Smeltie/Hyperion/Rendered Images/1.jpg

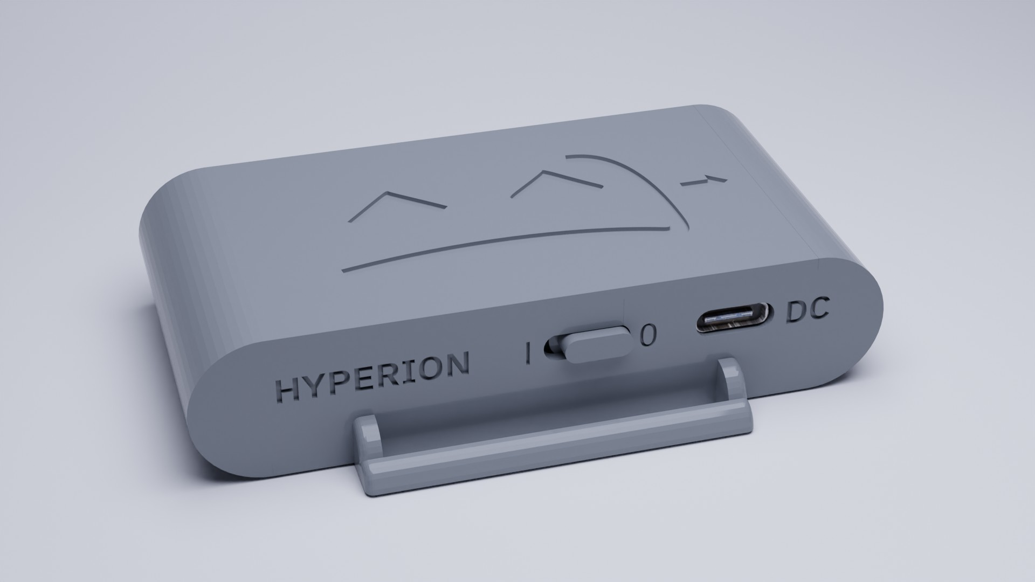
Rendered Images/1.jpg
