Smeltie/Hyperion/Rendered Images/2.jpg

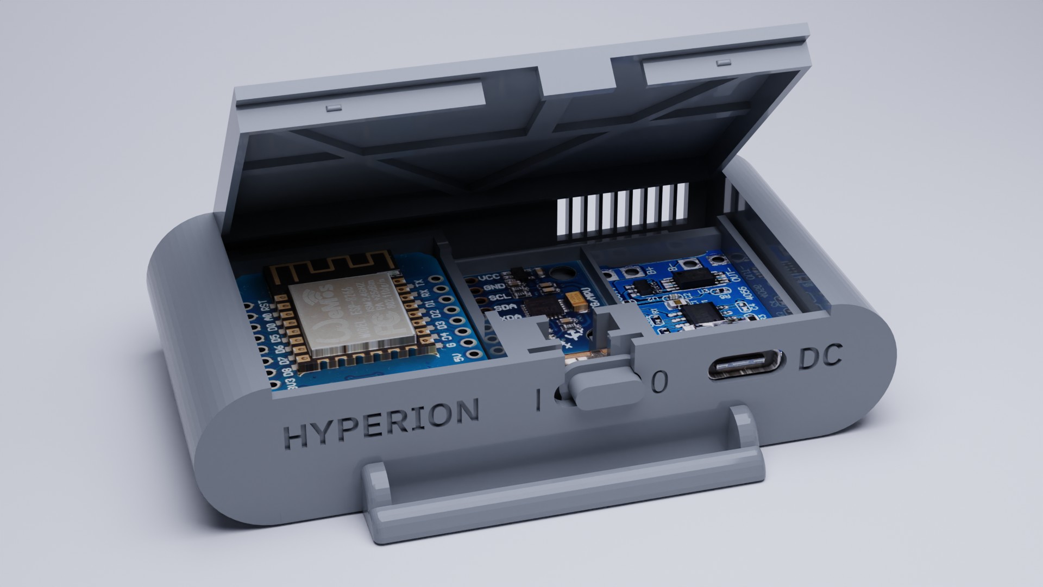
Rendered Images/2.jpg
