Smeltie/Hyperion/Rendered Images/3.jpg

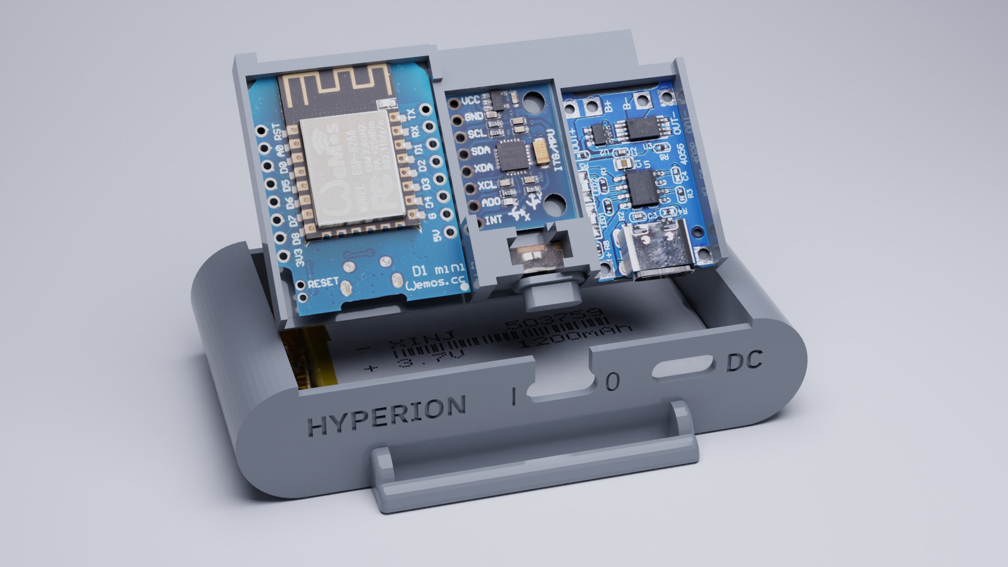
Rendered Images/3.jpg
