Smeltie/Hyperion/Rendered Images/4.jpg

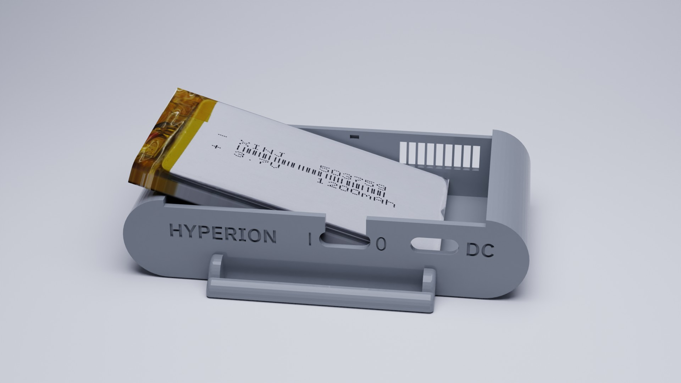
Rendered Images/4.jpg
