Smeltie/Hyperion/Rendered Images/5.jpg

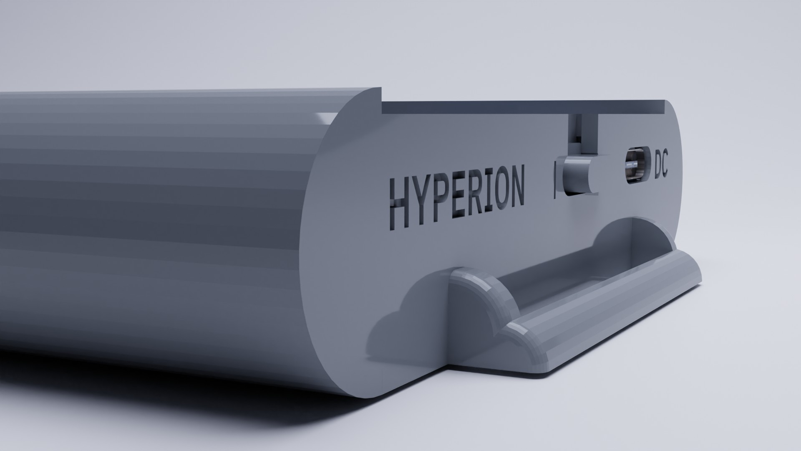
Rendered Images/5.jpg
