Smeltie/Hyperion/Rendered Images/6.jpg

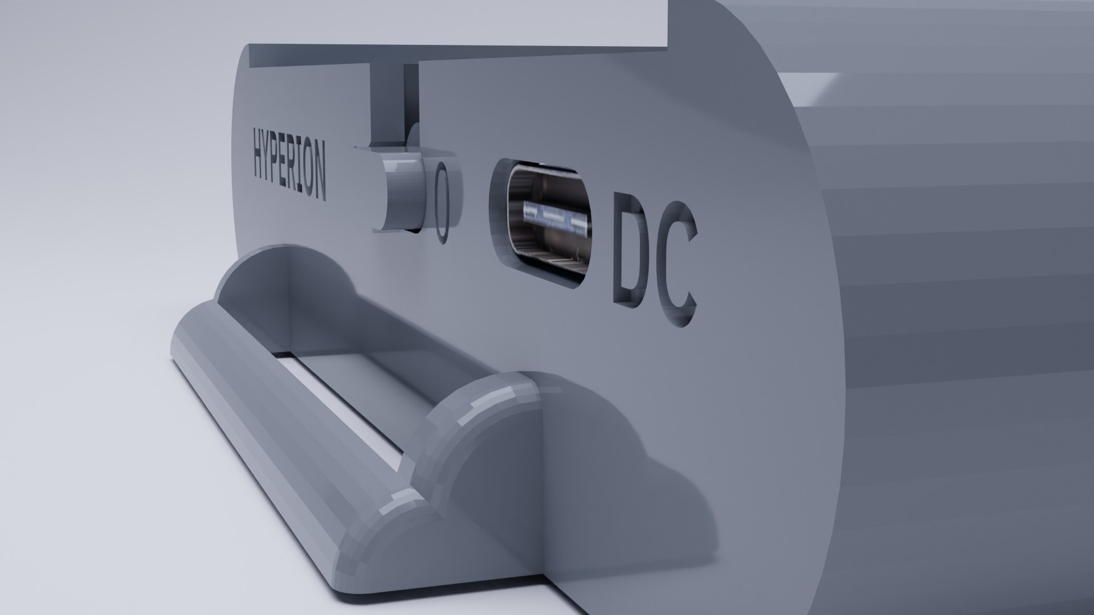
Rendered Images/6.jpg
