Smeltie/Hyperion/Rendered Images/7.jpg

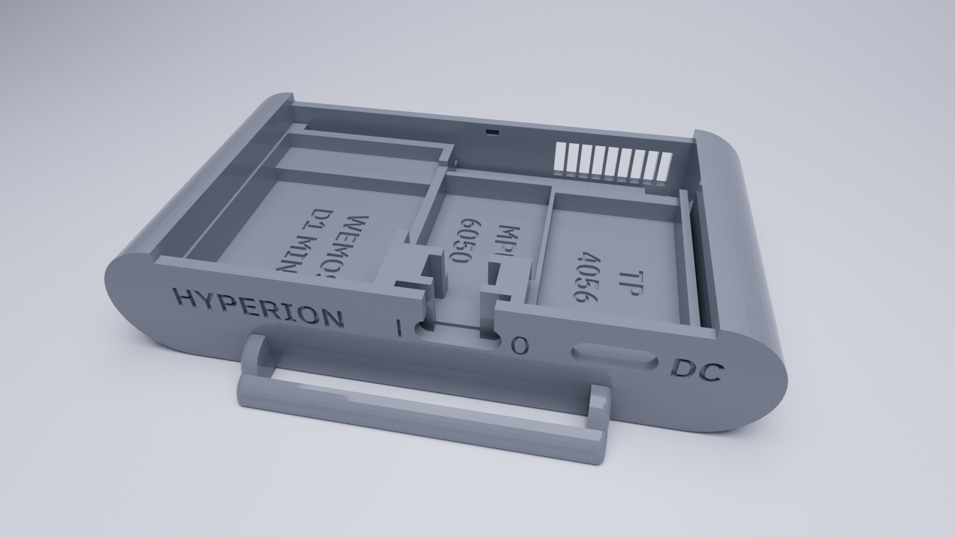
Rendered Images/7.jpg
