Smeltie/Hyperion/Untested/AUX_housing_BNO08x_25mm_wide.stl

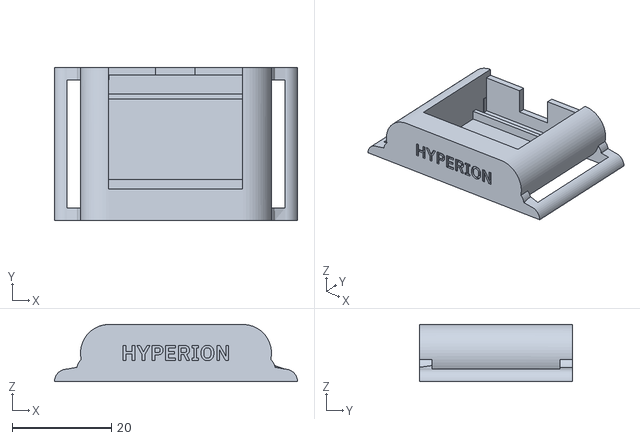
[picture p26: CAD file, 2022-06-16]
Untested/AUX_housing_BNO08x_25mm_wide.stl
49.0 x 30.8 x 11.5
