Smeltie/Hyperion/3D Models/WemosD1.obj

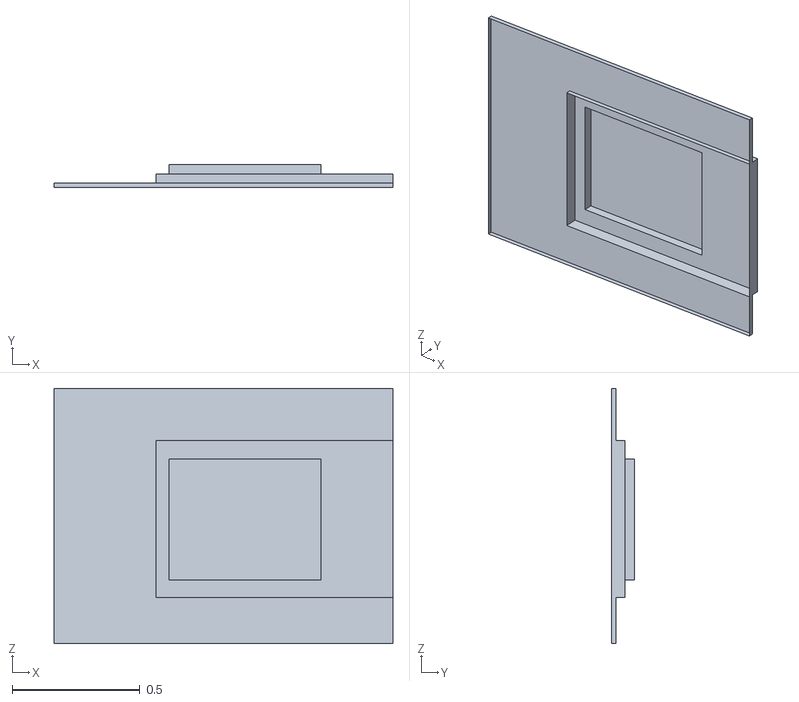
[picture p27: CAD file, 2022-01-04]
3D Models/WemosD1.obj
1.33 x 0.0918 x 1.00
