Smeltie/Hyperion/STL Files/804040_SS22F32/Tray_804040_BNO08x_SS22F32.stl

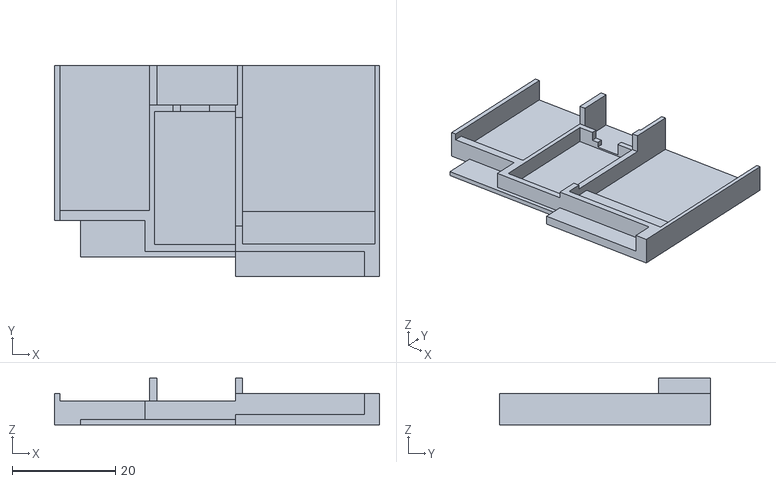
[picture p28: CAD file, 2022-02-25]
STL Files/804040_SS22F32/Tray_804040_BNO08x_SS22F32.stl
62.9 x 40.8 x 9.00
