Smeltie/Hyperion/STL Files/AUX_Housing.stl

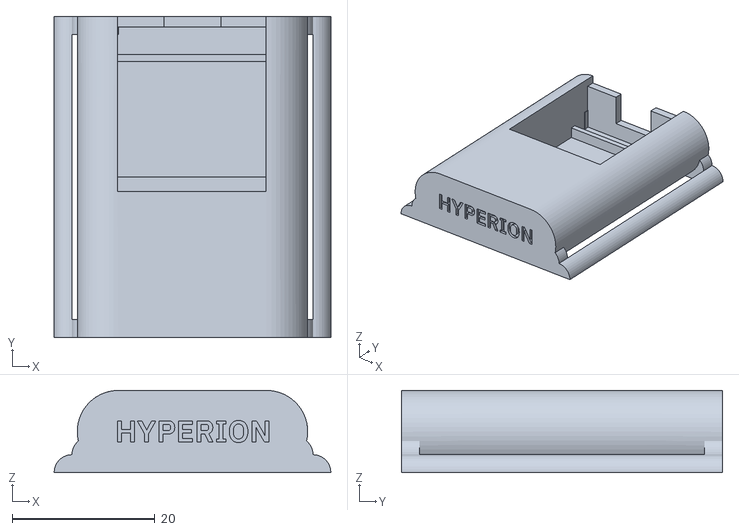
[picture p29: CAD file, 2022-02-25]
STL Files/AUX_Housing.stl
38.8 x 45.0 x 11.5
