Smeltie/Hyperion/Untested/AUX_housing_BNO08x_40mm_wide.stl

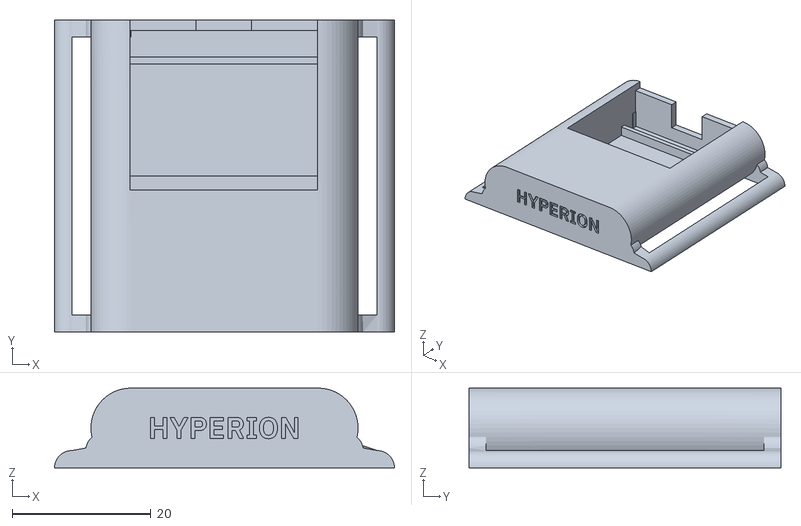
[picture p30: CAD file, 2022-06-16]
Untested/AUX_housing_BNO08x_40mm_wide.stl
49.0 x 45.0 x 11.5
