Smeltie/Hyperion/3D Models/pcb.obj

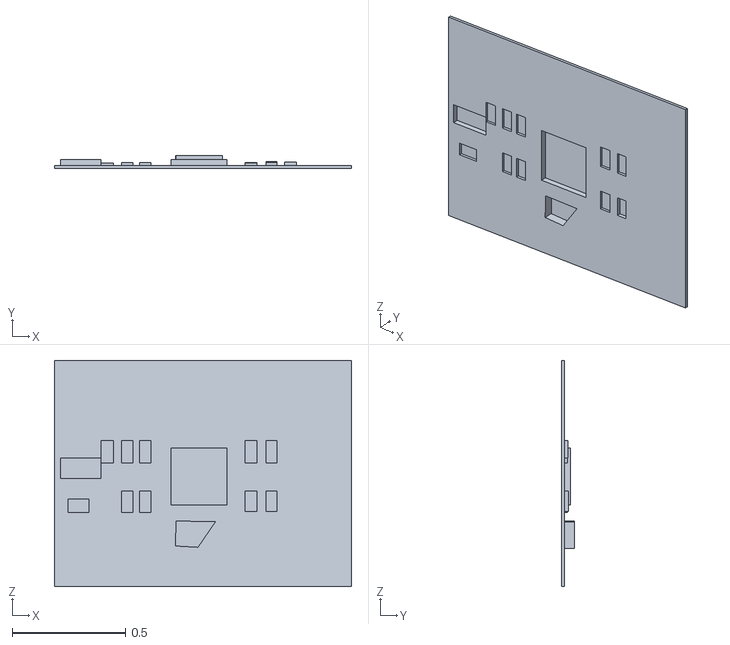
[picture p31: CAD file, 2022-01-04]
3D Models/pcb.obj
1.31 x 0.056 x 1.00
