Smeltie/Hyperion/STL Files/804040_SS22F32/Tray_804040_SS22F32.stl

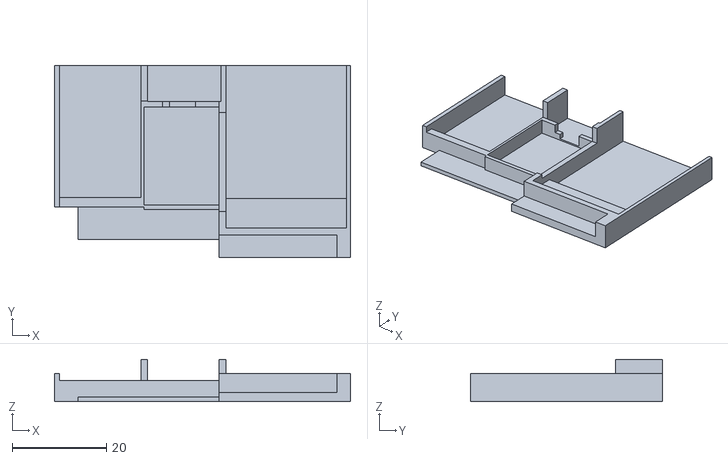
[picture p32: CAD file, 2022-02-16]
STL Files/804040_SS22F32/Tray_804040_SS22F32.stl
62.9 x 40.8 x 9.00
