Smeltie/Hyperion/STL Files/AUX_Housing_Lid.stl

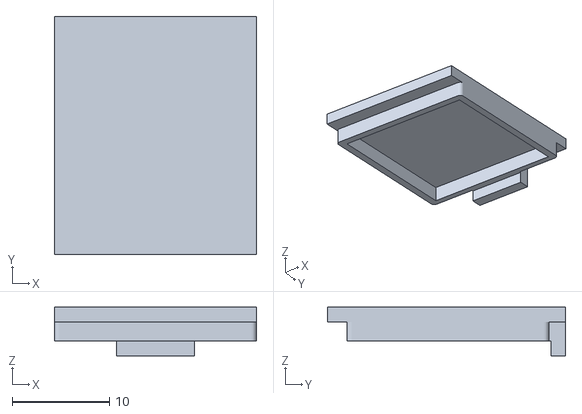
[picture p33: CAD file, 2022-02-25]
STL Files/AUX_Housing_Lid.stl
20.8 x 24.5 x 5.00
