Smeltie/Hyperion/Untested/AUX_Housing_BNO08x.stl

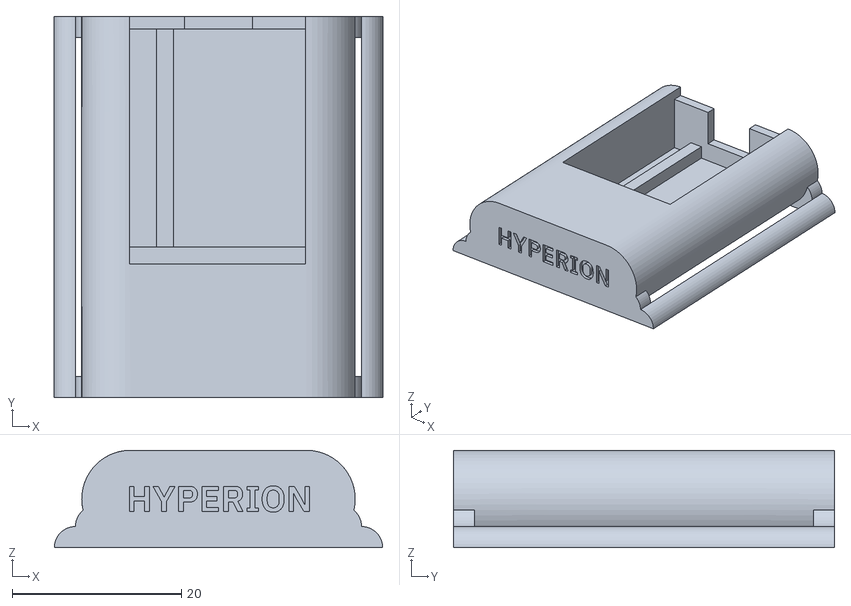
[picture p34: CAD file, 2022-02-25]
Untested/AUX_Housing_BNO08x.stl
38.8 x 45.0 x 11.5
