Smeltie/Hyperion/STL Files/503759/Lid_503759_AUX_Blank.stl

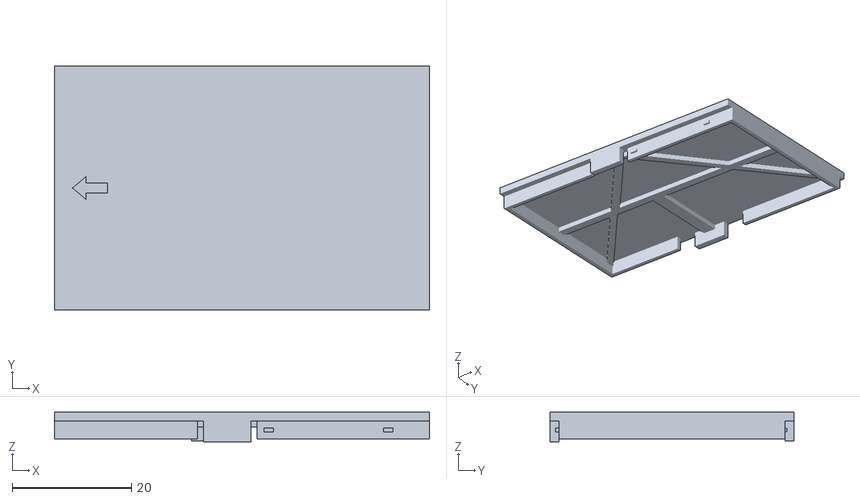
[picture p35: CAD file, 2022-01-04]
STL Files/503759/Lid_503759_AUX_Blank.stl
63.0 x 41.0 x 5.00
