Smeltie/Hyperion/STL Files/804040/Lid_804040_AUX_Blank.stl

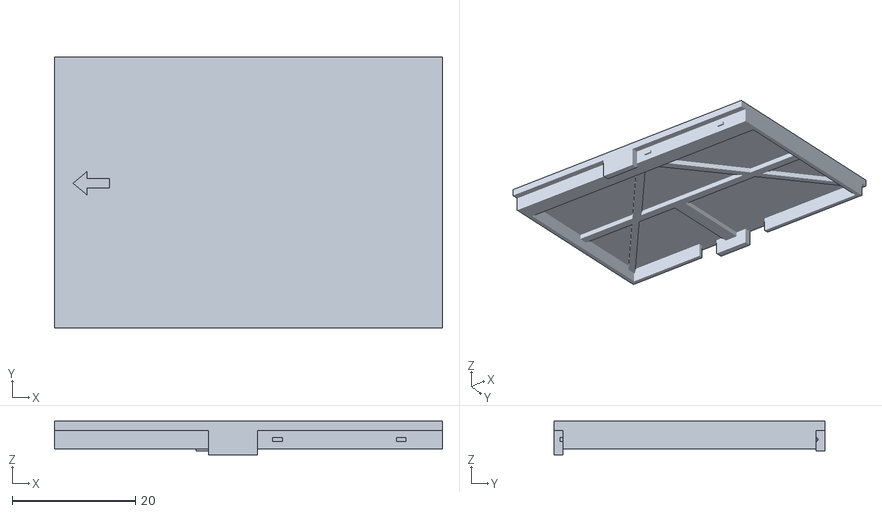
[picture p36: CAD file, 2022-01-04]
STL Files/804040/Lid_804040_AUX_Blank.stl
63.0 x 44.0 x 5.50
