Smeltie/Hyperion/STL Files/Switch.stl

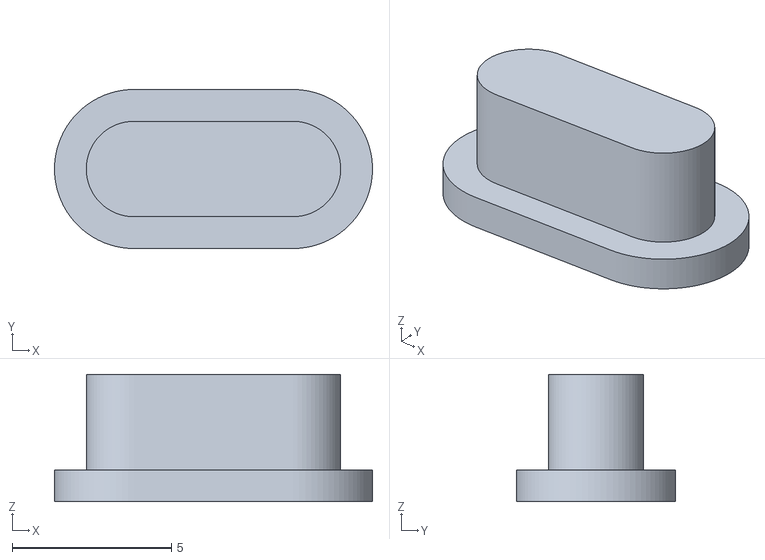
[picture p37: CAD file, 2022-01-04]
STL Files/Switch.stl
10.00 x 5.00 x 4.00
