Smeltie/Hyperion/Untested/AUX_Housing_Lid_BNO08x.stl

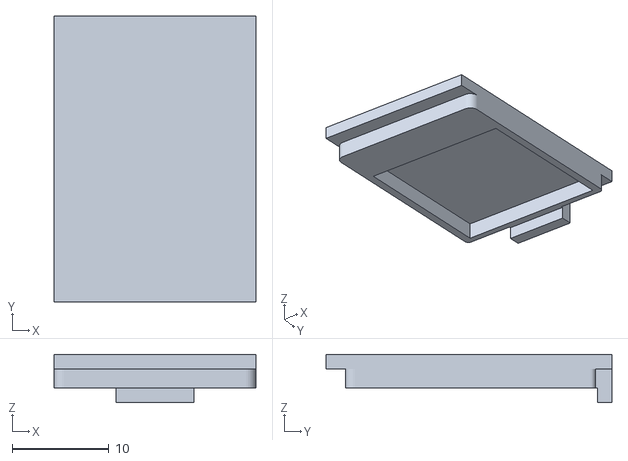
[picture p38: CAD file, 2022-02-25]
Untested/AUX_Housing_Lid_BNO08x.stl
20.8 x 29.5 x 5.00
