Smeltie/Hyperion/STL Files/503759_SS22F32/Lid_503759_S22F32_Blank.stl

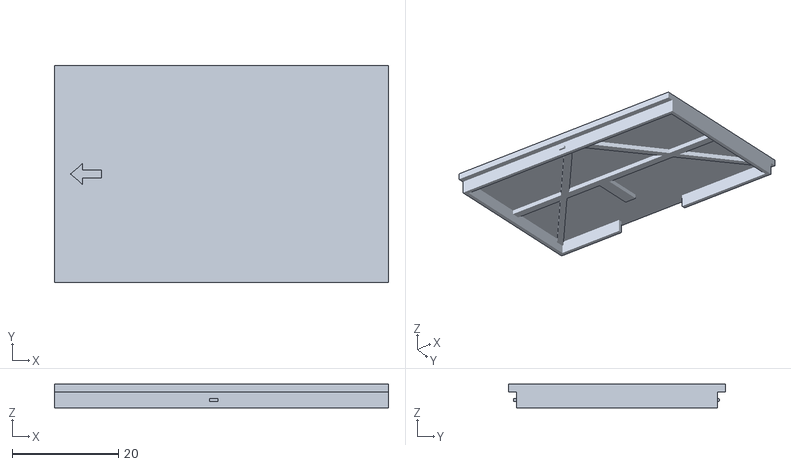
[picture p40: CAD file, 2022-01-13]
STL Files/503759_SS22F32/Lid_503759_S22F32_Blank.stl
63.0 x 41.0 x 4.50
