Smeltie/Hyperion/STL Files/804040/Lid_804040_AUX_Slime.stl

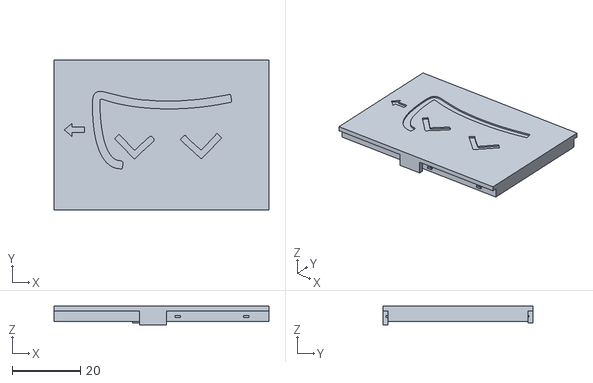
[picture p41: CAD file, 2022-01-04]
STL Files/804040/Lid_804040_AUX_Slime.stl
63.0 x 44.0 x 5.50
