Smeltie/Hyperion/STL Files/503759/Lid_503759_Slime.stl

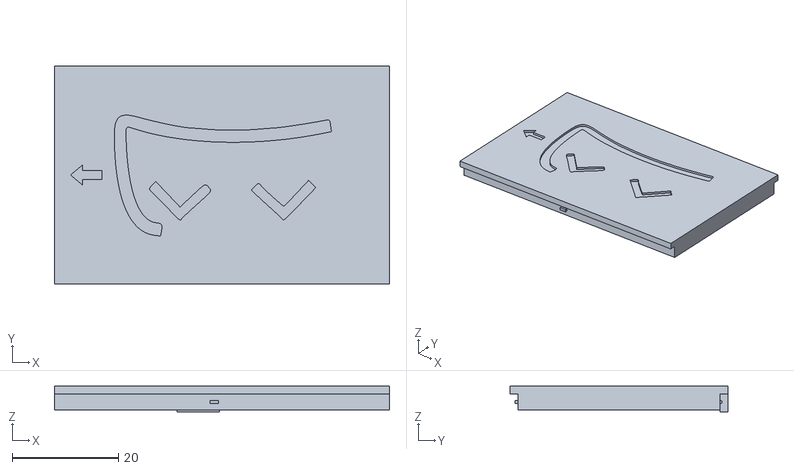
[picture p42: CAD file, 2022-01-04]
STL Files/503759/Lid_503759_Slime.stl
63.0 x 41.0 x 4.88
