Smeltie/Hyperion/STL Files/804040/Lid_804040_Slime.stl

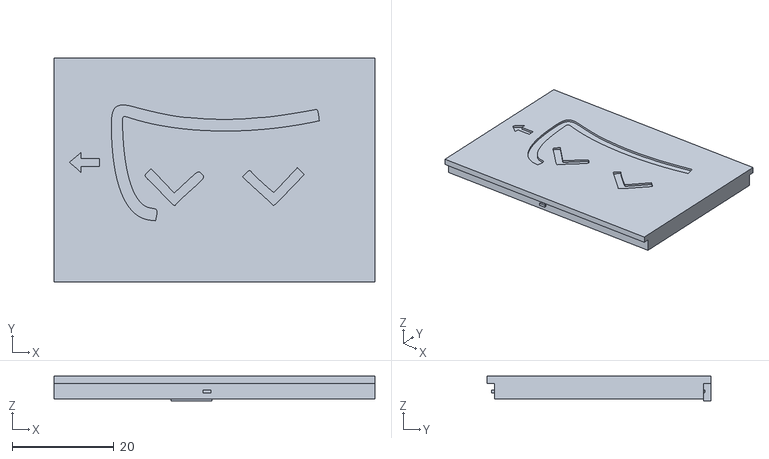
[picture p43: CAD file, 2022-01-04]
STL Files/804040/Lid_804040_Slime.stl
63.0 x 44.0 x 4.88
