Smeltie/Hyperion/STL Files/804040_SS22F32/Lid_804040_SS22F32_AUX_Blank.stl

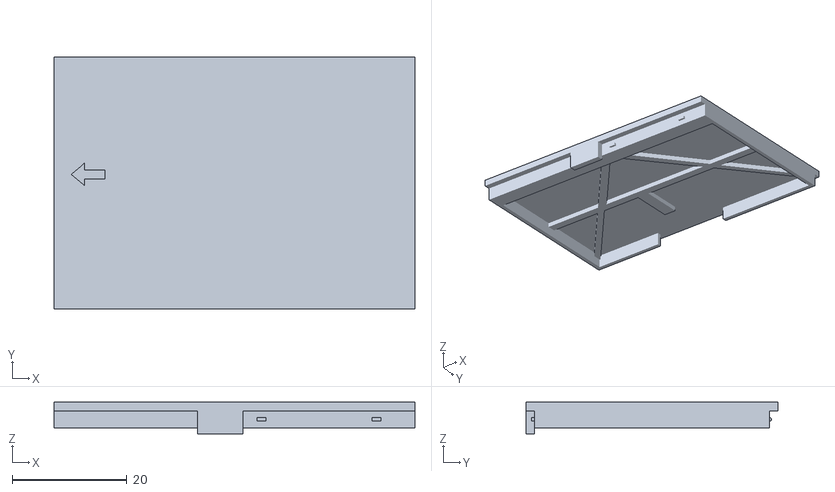
[picture p44: CAD file, 2022-01-13]
STL Files/804040_SS22F32/Lid_804040_SS22F32_AUX_Blank.stl
63.0 x 44.0 x 5.50
