Smeltie/Hyperion/STL Files/503759/Lid_503759_Blank.stl

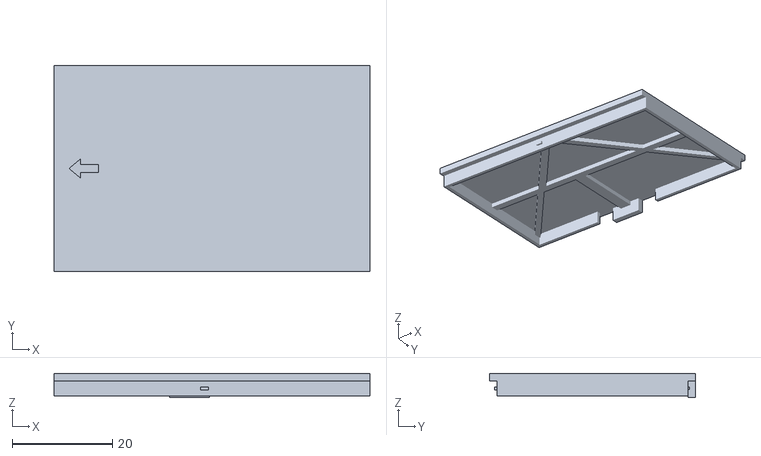
[picture p45: CAD file, 2022-01-04]
STL Files/503759/Lid_503759_Blank.stl
63.0 x 41.0 x 4.88
