Smeltie/Hyperion/STL Files/503759_SS22F32/Lid_503759_S22F32_AUX_Blank.stl

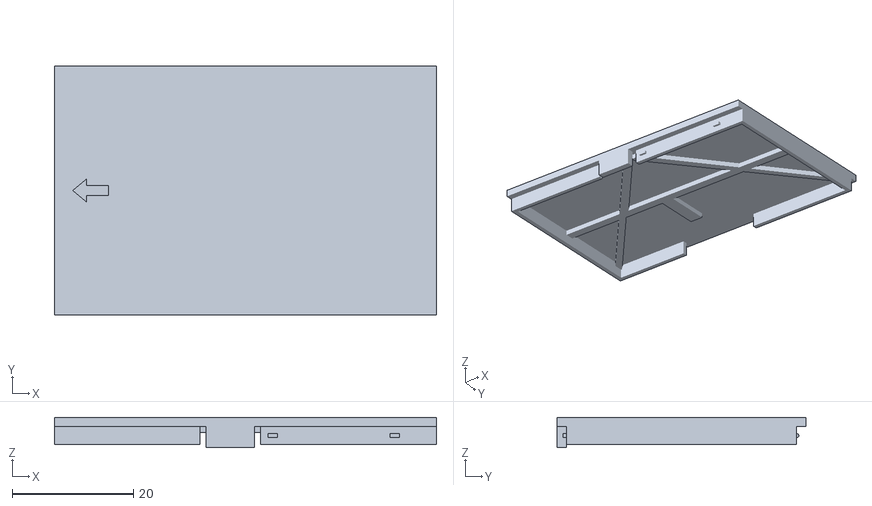
[picture p46: CAD file, 2022-01-13]
STL Files/503759_SS22F32/Lid_503759_S22F32_AUX_Blank.stl
63.0 x 41.0 x 5.00
