Smeltie/Hyperion/STL Files/804040/Lid_804040_Blank.stl

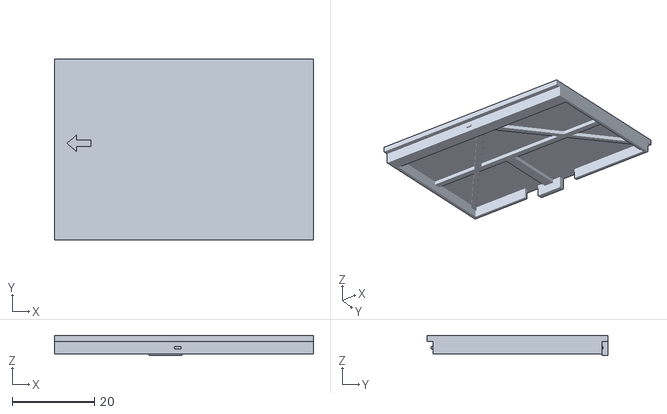
[picture p47: CAD file, 2022-01-04]
STL Files/804040/Lid_804040_Blank.stl
63.0 x 44.0 x 4.88
