Smeltie/Hyperion/STL Files/503759_SS22F32/Lid_503759_S22F32_Slime.stl

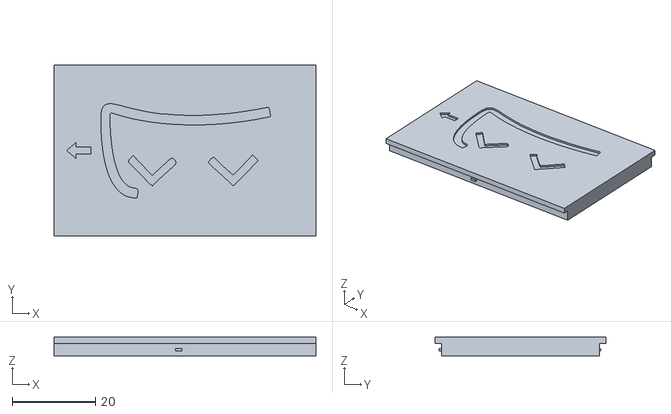
[picture p49: CAD file, 2022-01-11]
STL Files/503759_SS22F32/Lid_503759_S22F32_Slime.stl
63.0 x 41.0 x 4.50
